opensourcebeehives/Hive_ColoradoTopBar/Images/AKER - Colorado Top Bar - v1.0 - Master Assembly-min.jpg

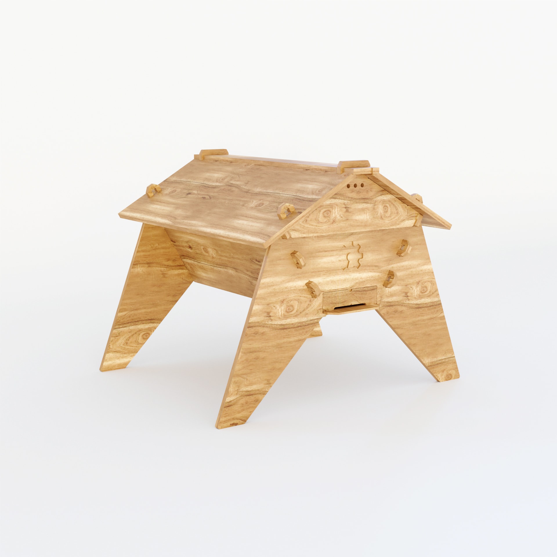
Images/AKER - Colorado Top Bar - v1.0 - Master Assembly-min.jpg
